andydoro/WordClock-NeoMatrix8x8/WordClock_NeoMatrix8x8/flashWords.ino

// test function, can we draw those words correctly?

void flashWords(void) {

  ANDYDORO;  // my name hidden in here
  applyMask();
  delay(FLASHDELAY * 2);

  MFIVE;
  applyMask();
  delay(FLASHDELAY);

  MTEN;
  applyMask();
  delay(FLASHDELAY);

  AQUARTER;
  applyMask();
  delay(FLASHDELAY);

  TWENTY;
  applyMask();
  delay(FLASHDELAY);

  HALF;
  applyMask();
  delay(FLASHDELAY);

  TO;
  applyMask();
  delay(FLASHDELAY);

  PAST;
  applyMask();
  delay(FLASHDELAY);

  ONE;
  applyMask();
  delay(FLASHDELAY);

  TWO;
  applyMask();
  delay(FLASHDELAY);

  THREE;
  applyMask();
  delay(FLASHDELAY);

  FOUR;
  applyMask();
  delay(FLASHDELAY);

  FIVE;
  applyMask();
  delay(FLASHDELAY);

  SIX;
  applyMask();
  delay(FLASHDELAY);

  SEVEN;
  applyMask();
  delay(FLASHDELAY);

  EIGHT;
  applyMask();
  delay(FLASHDELAY);

  NINE;
  applyMask();
  delay(FLASHDELAY);

  TEN;
  applyMask();
  delay(FLASHDELAY);

  ELEVEN;
  applyMask();
  delay(FLASHDELAY);

  TWELVE;
  applyMask();
  delay(FLASHDELAY);

  // blank for a bit
  applyMask();
  delay(FLASHDELAY);

}
